xrobot-org/atom-sdk/stm32_can_example/Core/Inc/main.h

#define LED_RUN_Pin GPIO_PIN_0
#define LED_RUN_GPIO_Port GPIOB
